IljaRukin/3D_line_laser_scanner/line_3D_scanner.jpeg

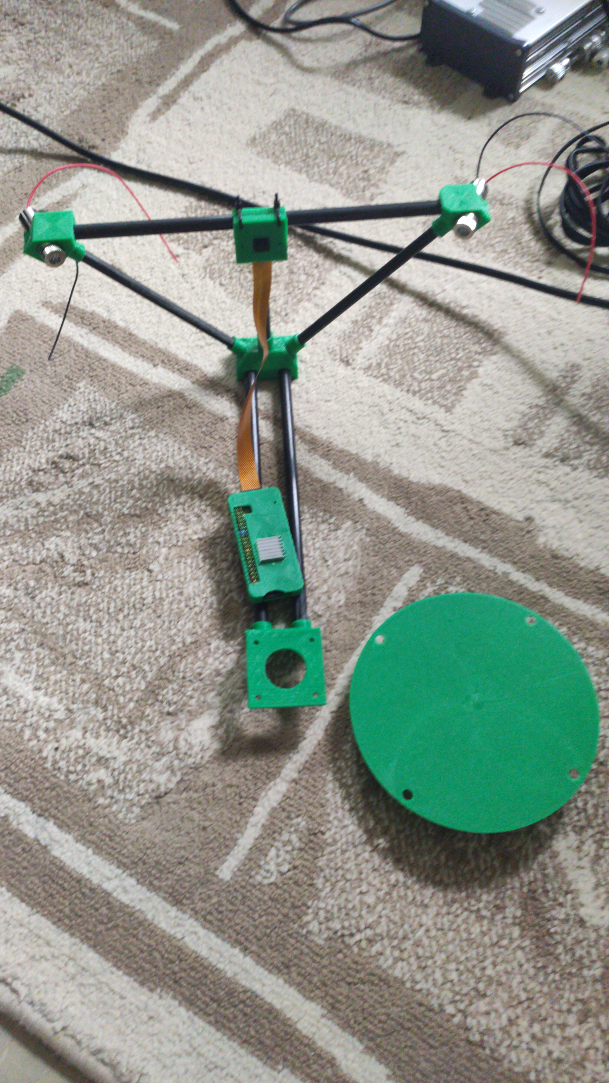
line_3D_scanner.jpeg
