IljaRukin/3D_line_laser_scanner/rectification/images/image2.jpg

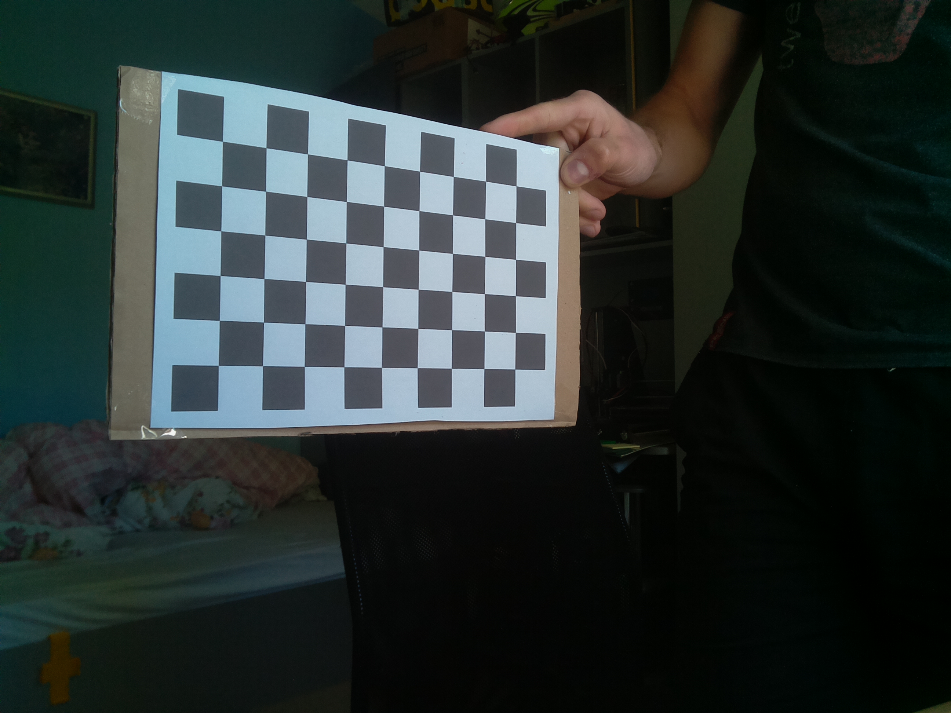
rectification/images/image2.jpg
