IljaRukin/3D_line_laser_scanner/rectification/images/image3.jpg

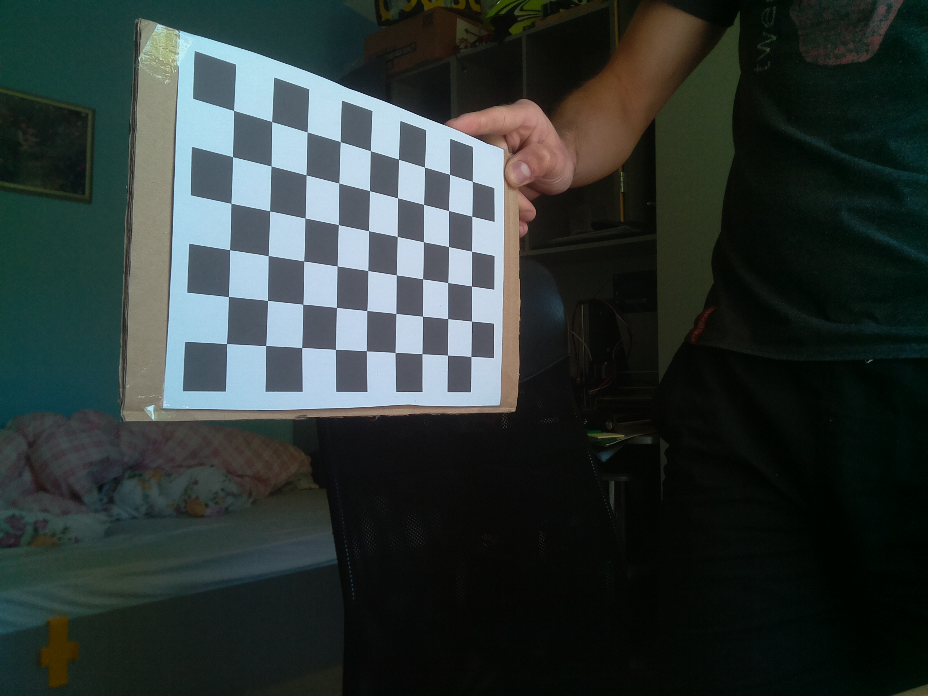
rectification/images/image3.jpg
