IljaRukin/3D_line_laser_scanner/rectification/images/image4.jpg

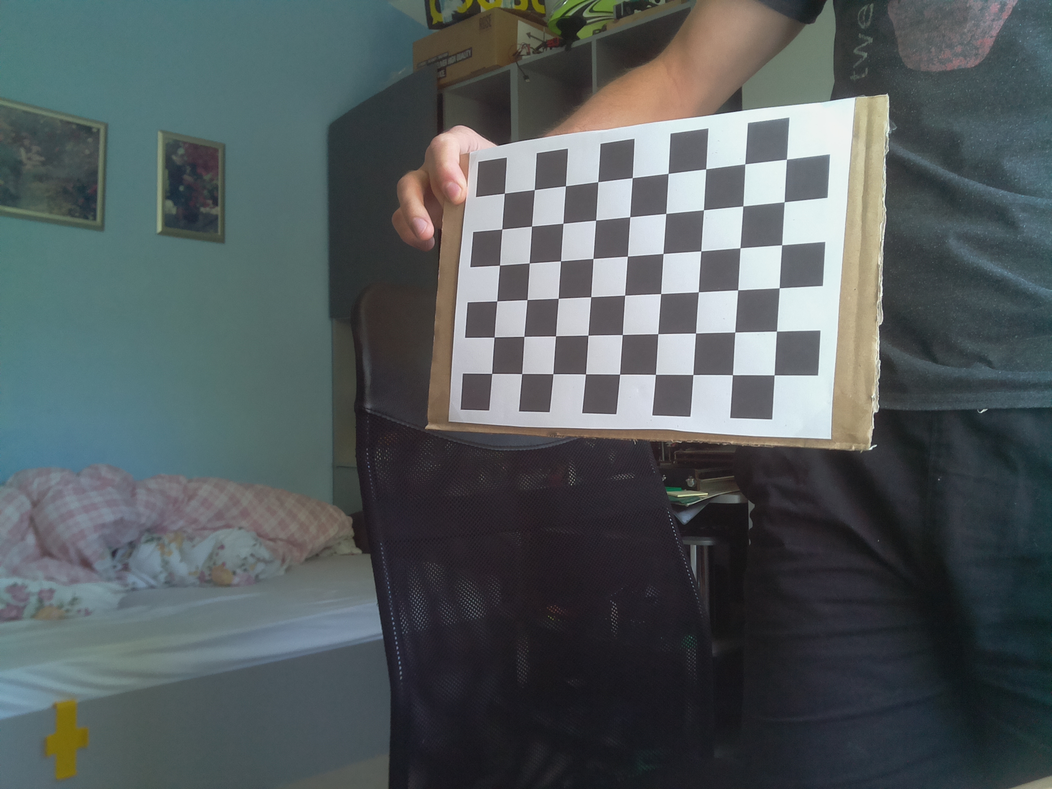
rectification/images/image4.jpg
