IljaRukin/3D_line_laser_scanner/rectification/images/image7.jpg

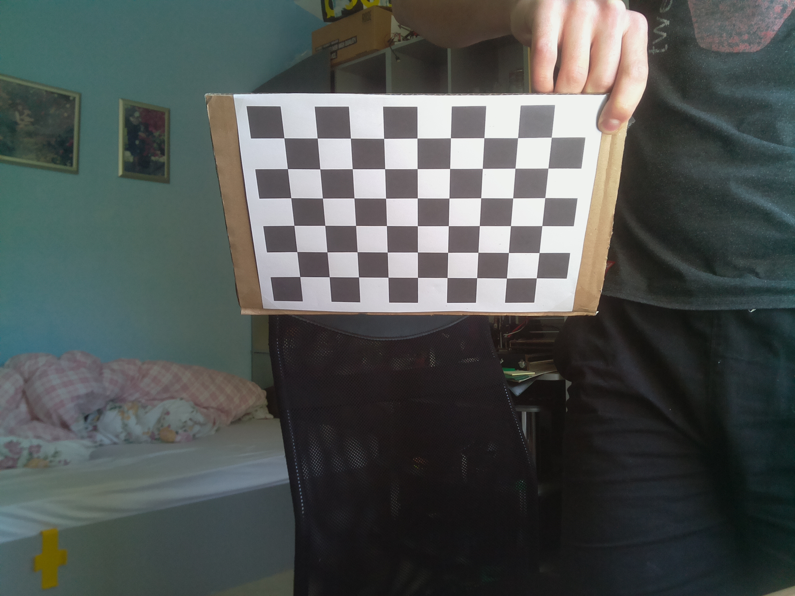
rectification/images/image7.jpg
