IljaRukin/3D_line_laser_scanner/rectification/images/image8.jpg

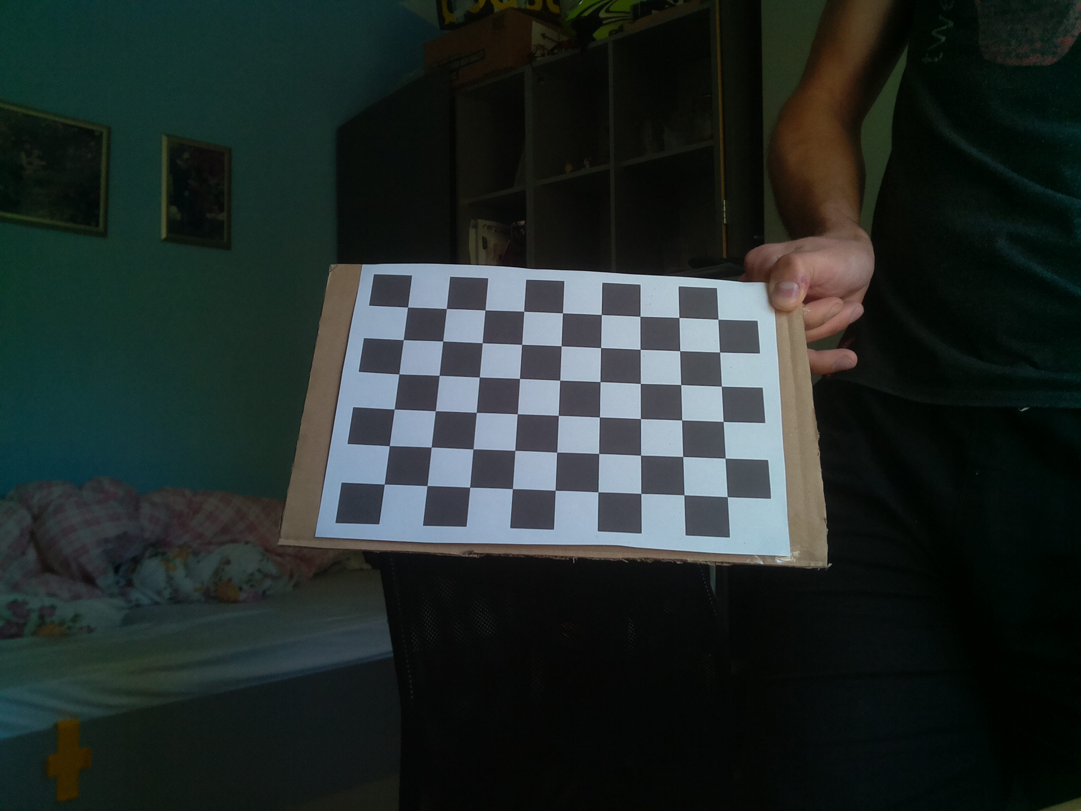
rectification/images/image8.jpg
