IljaRukin/3D_line_laser_scanner/rectification/images/image9.jpg

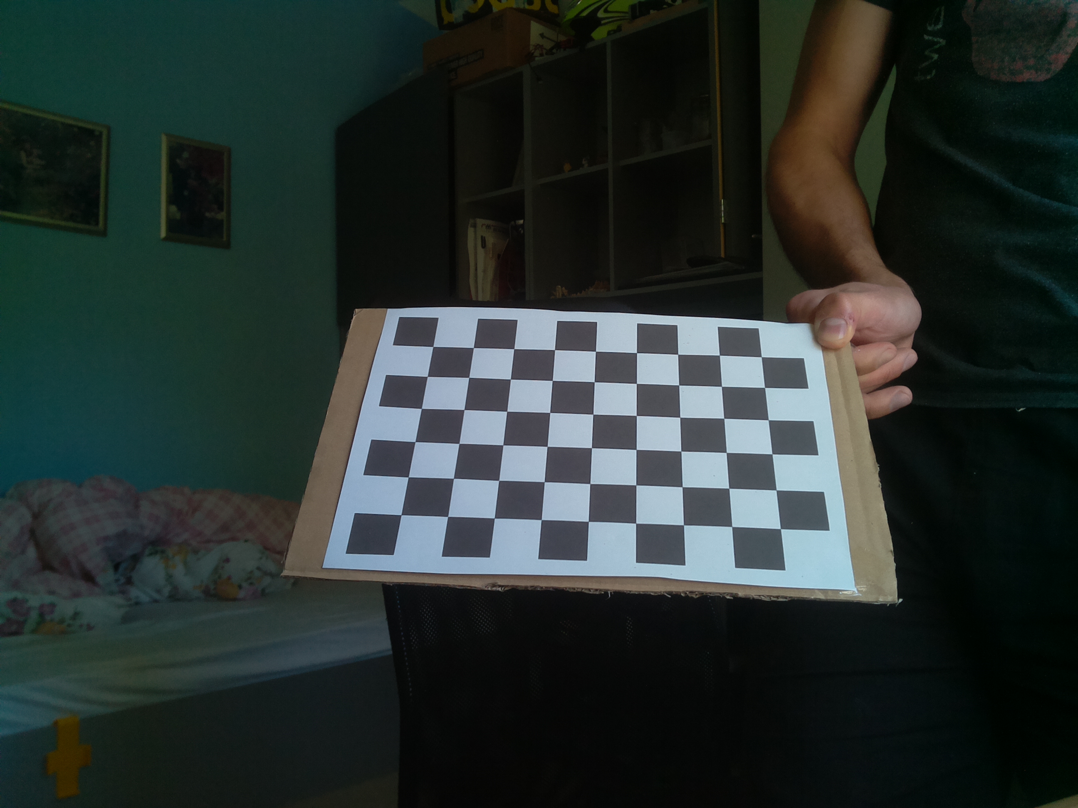
rectification/images/image9.jpg
