IljaRukin/3D_line_laser_scanner/rectification/images/image10.jpg

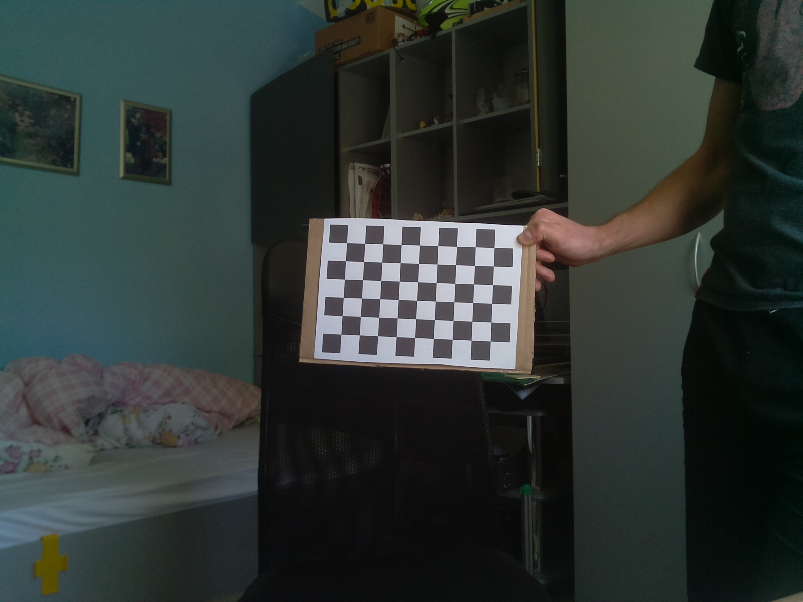
rectification/images/image10.jpg
