IljaRukin/3D_line_laser_scanner/rectification/images/image11.jpg

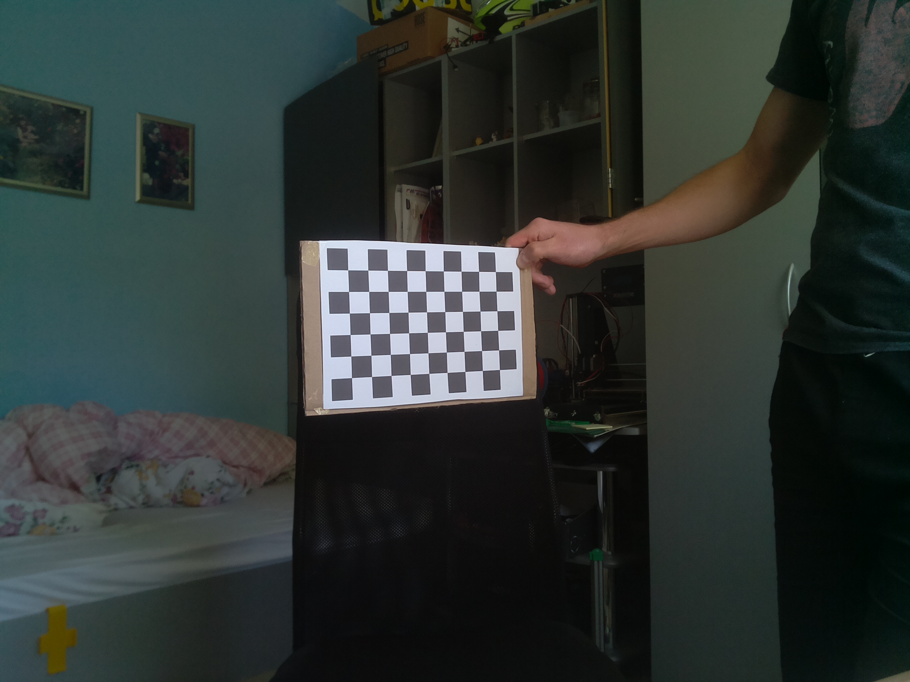
rectification/images/image11.jpg
