IljaRukin/3D_line_laser_scanner/rectification/images/image13.jpg

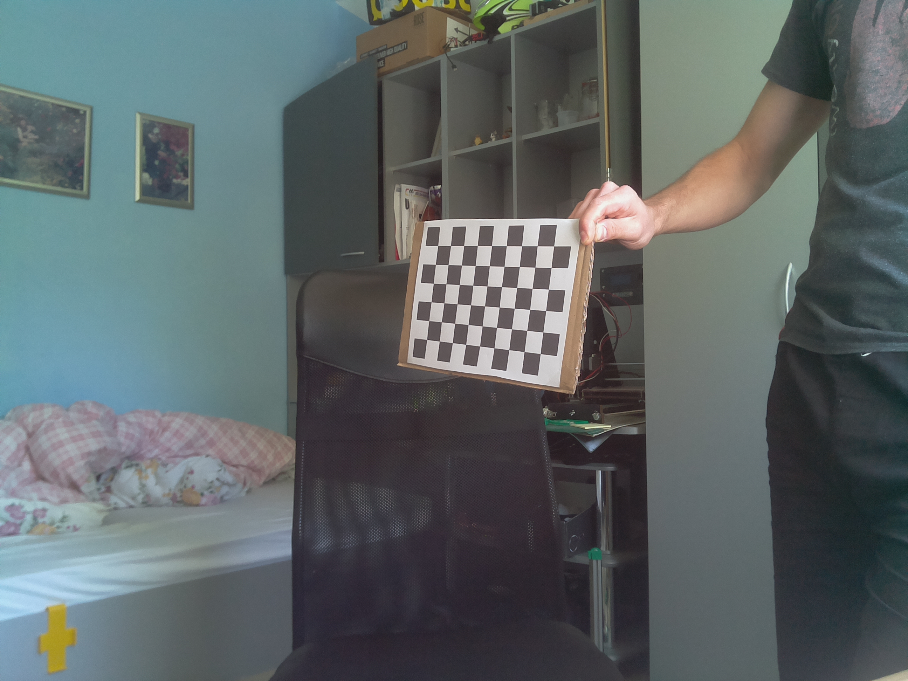
rectification/images/image13.jpg
