IljaRukin/3D_line_laser_scanner/rectification/images/image15.jpg

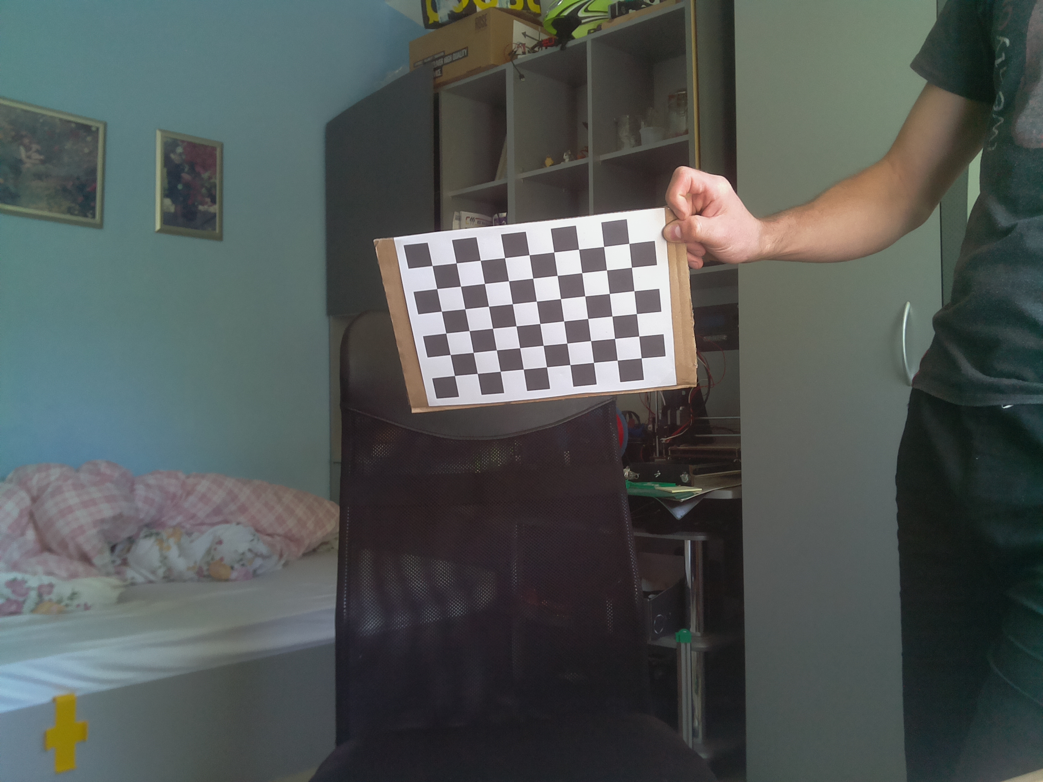
rectification/images/image15.jpg
