IljaRukin/3D_line_laser_scanner/rectification/images/image17.jpg

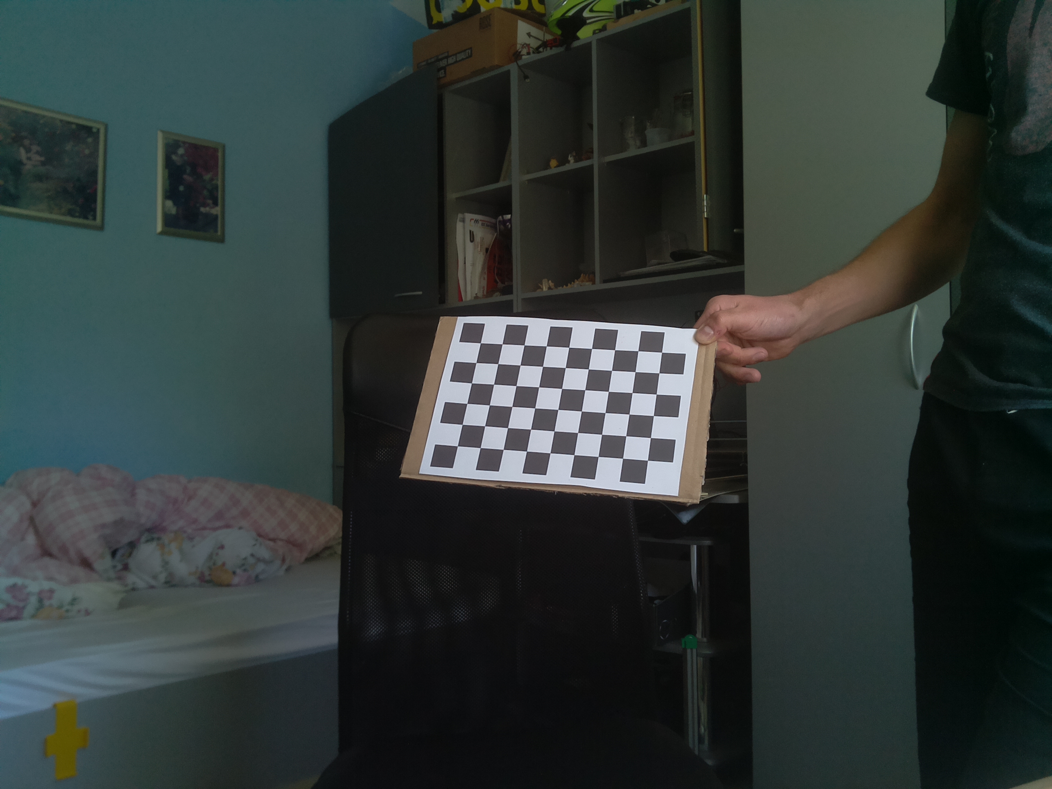
rectification/images/image17.jpg
