IljaRukin/3D_line_laser_scanner/rectification/images/image18.jpg

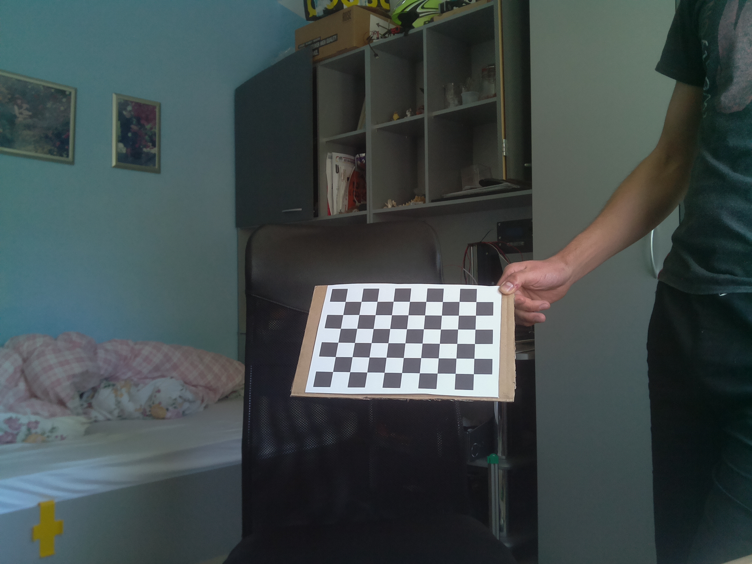
rectification/images/image18.jpg
