IljaRukin/3D_line_laser_scanner/rectification/images/image19.jpg

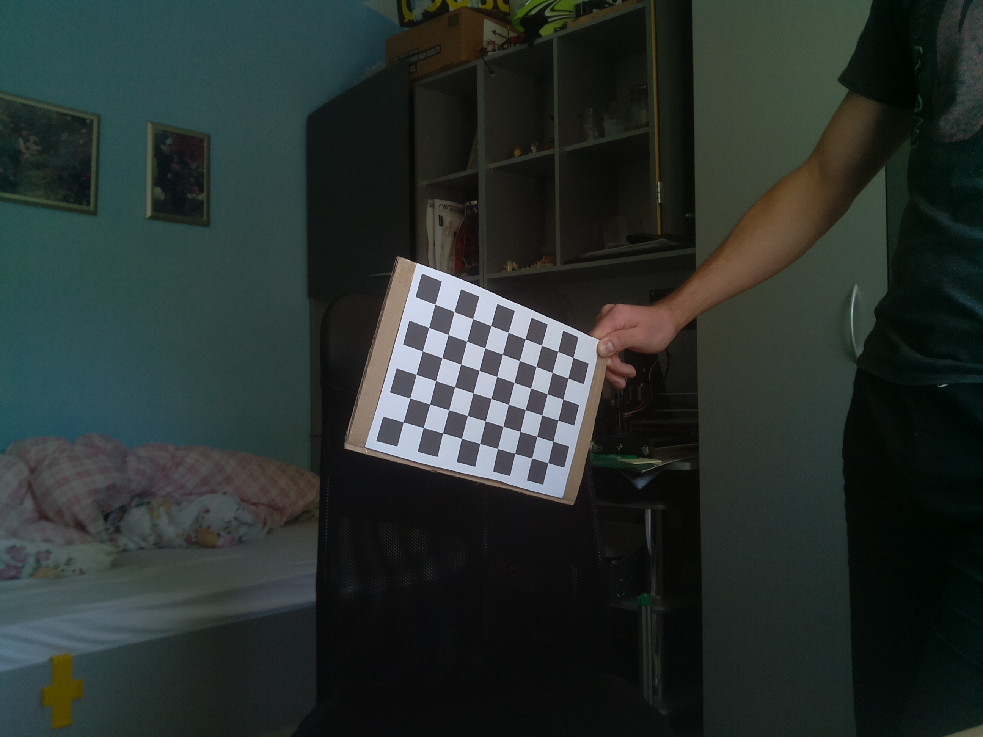
rectification/images/image19.jpg
