IljaRukin/3D_line_laser_scanner/rectification/images/image21.jpg

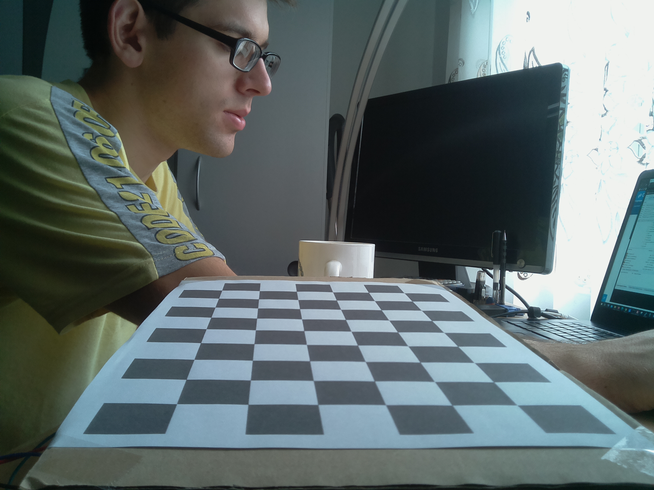
rectification/images/image21.jpg
