IljaRukin/3D_line_laser_scanner/rectification/images/image22.jpg

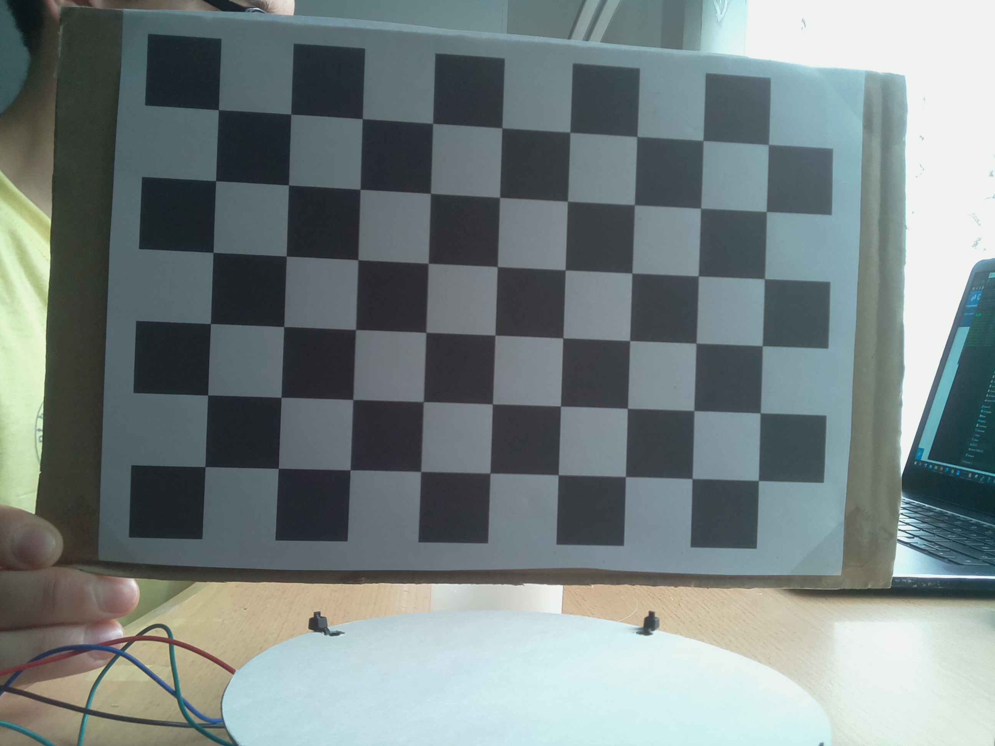
rectification/images/image22.jpg
