IljaRukin/3D_line_laser_scanner/rectification/images/image23.jpg

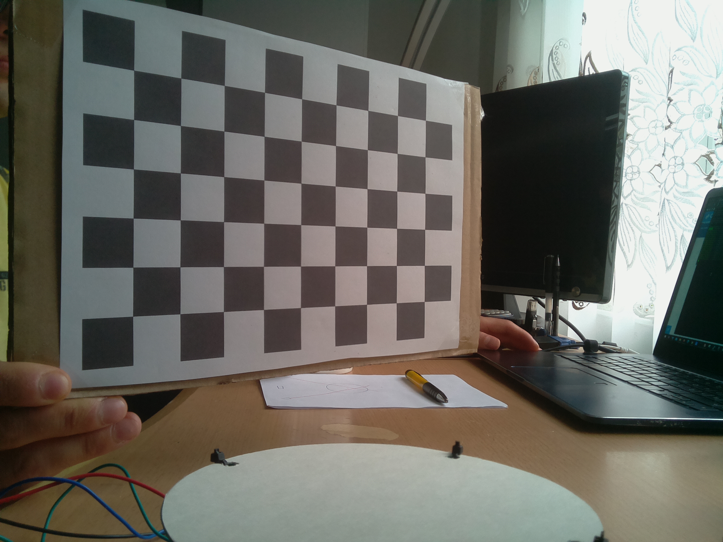
rectification/images/image23.jpg
