IljaRukin/3D_line_laser_scanner/rectification/images/image24.jpg

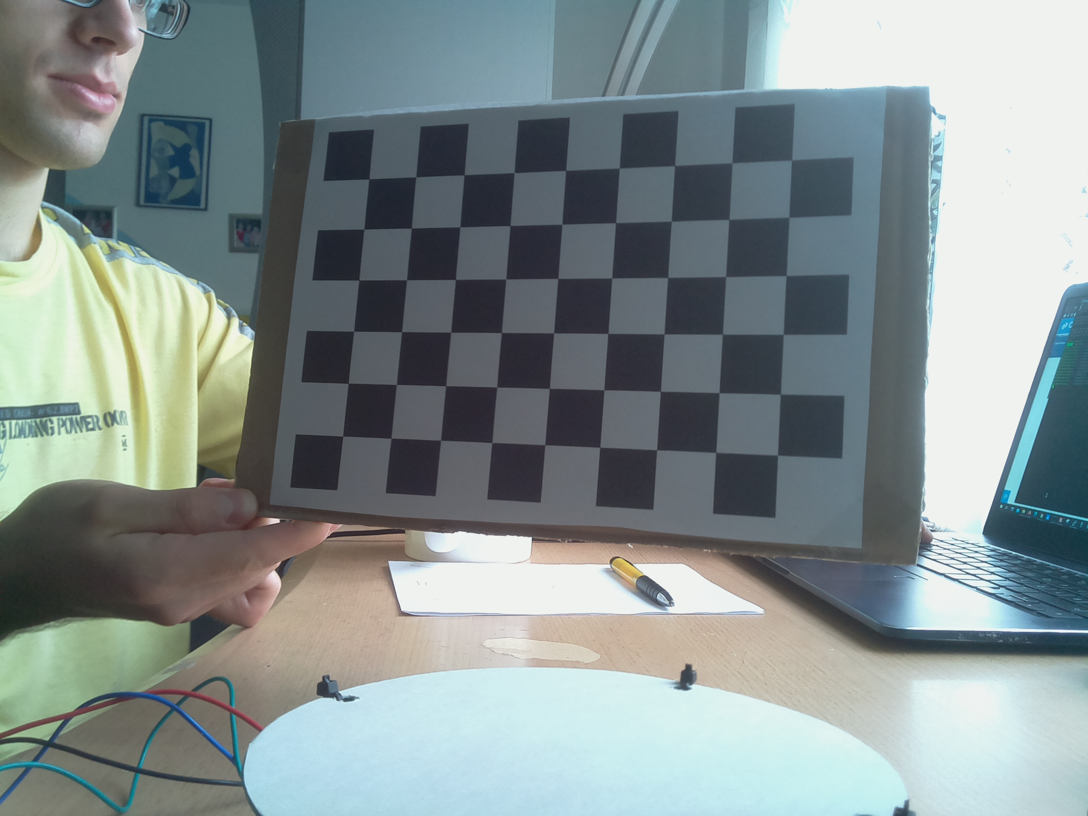
rectification/images/image24.jpg
