IljaRukin/3D_line_laser_scanner/scan_images/img_l_000.jpg

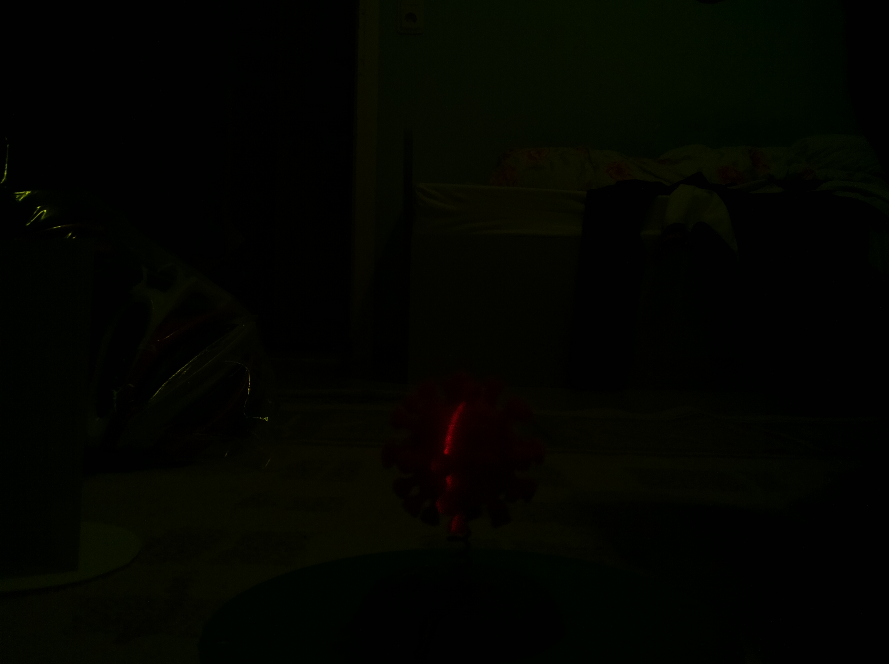
scan_images/img_l_000.jpg
